p2made/P2-Camp-Kitchen/docs/Sheet-Metal.pdf

1. Number Plate Mount
2. Battery Clamp
3. Fridge Tray Rails
4. Stainless Steel Top
5. Splash Back Cover

To be attached to the back frame. Drawn as 1 mm sheet metal.

# Sheet Metal

# Number Plate Mount

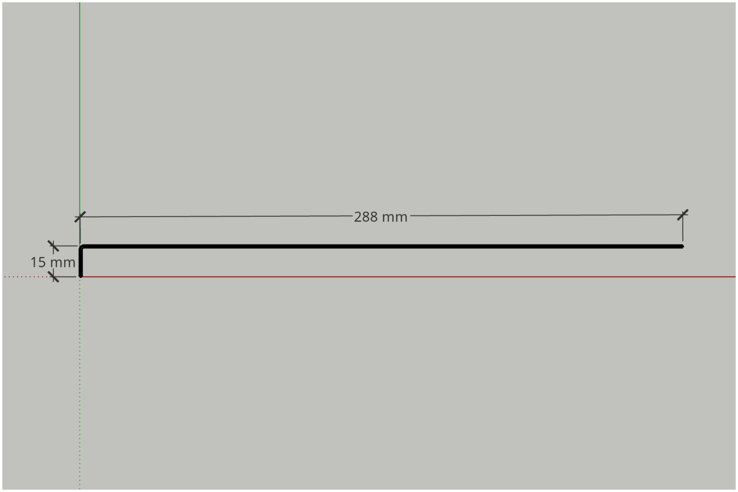
[picture p41: figure]
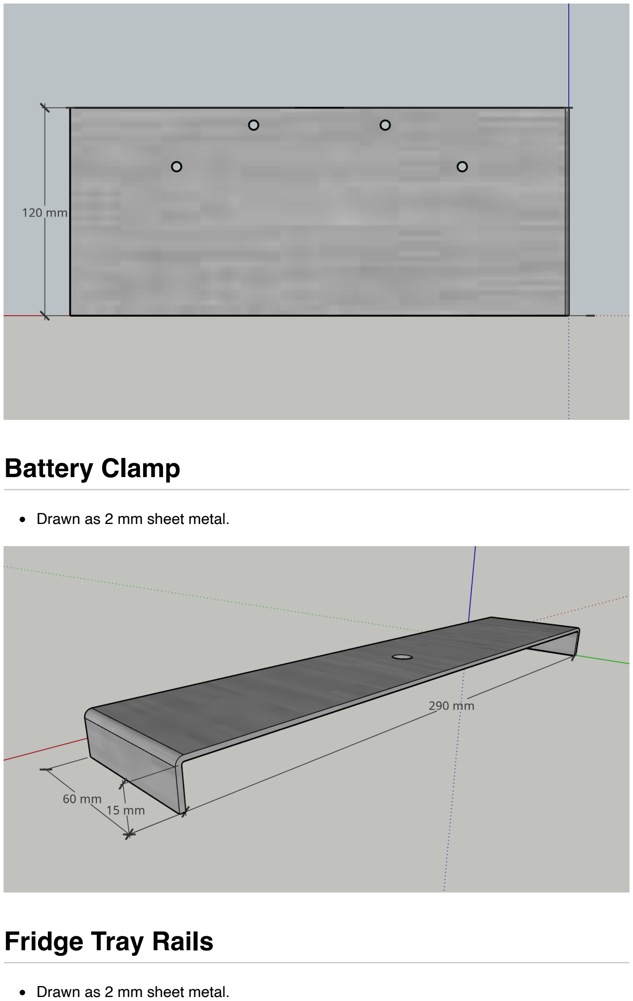
[picture p42: page 2]

Drawn as 2 mm sheet metal.

Drawn as 2 mm sheet metal.

# Battery Clamp

# Fridge Tray Rails

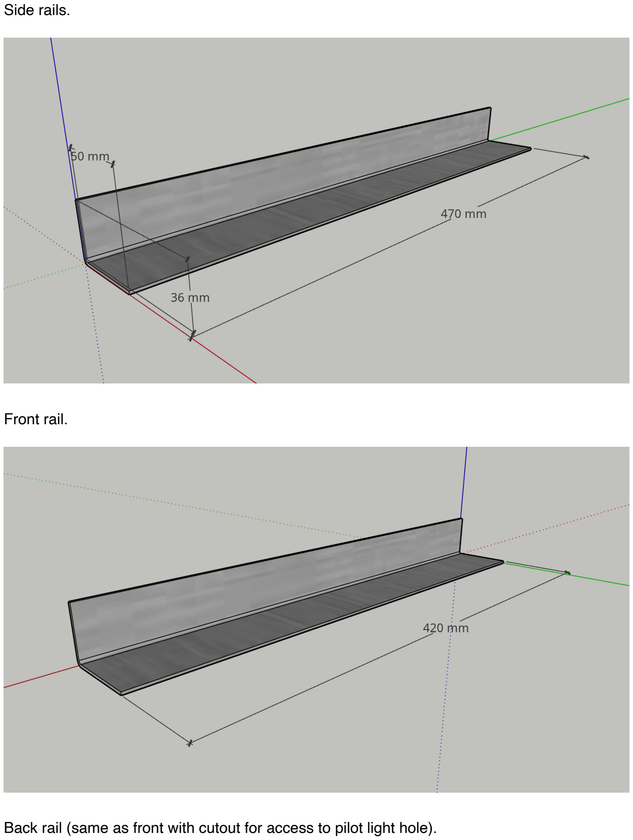
[picture p43: page 3]

Side rails.

Front rail.

Back rail (same as front with cutout for access to pilot light hole).

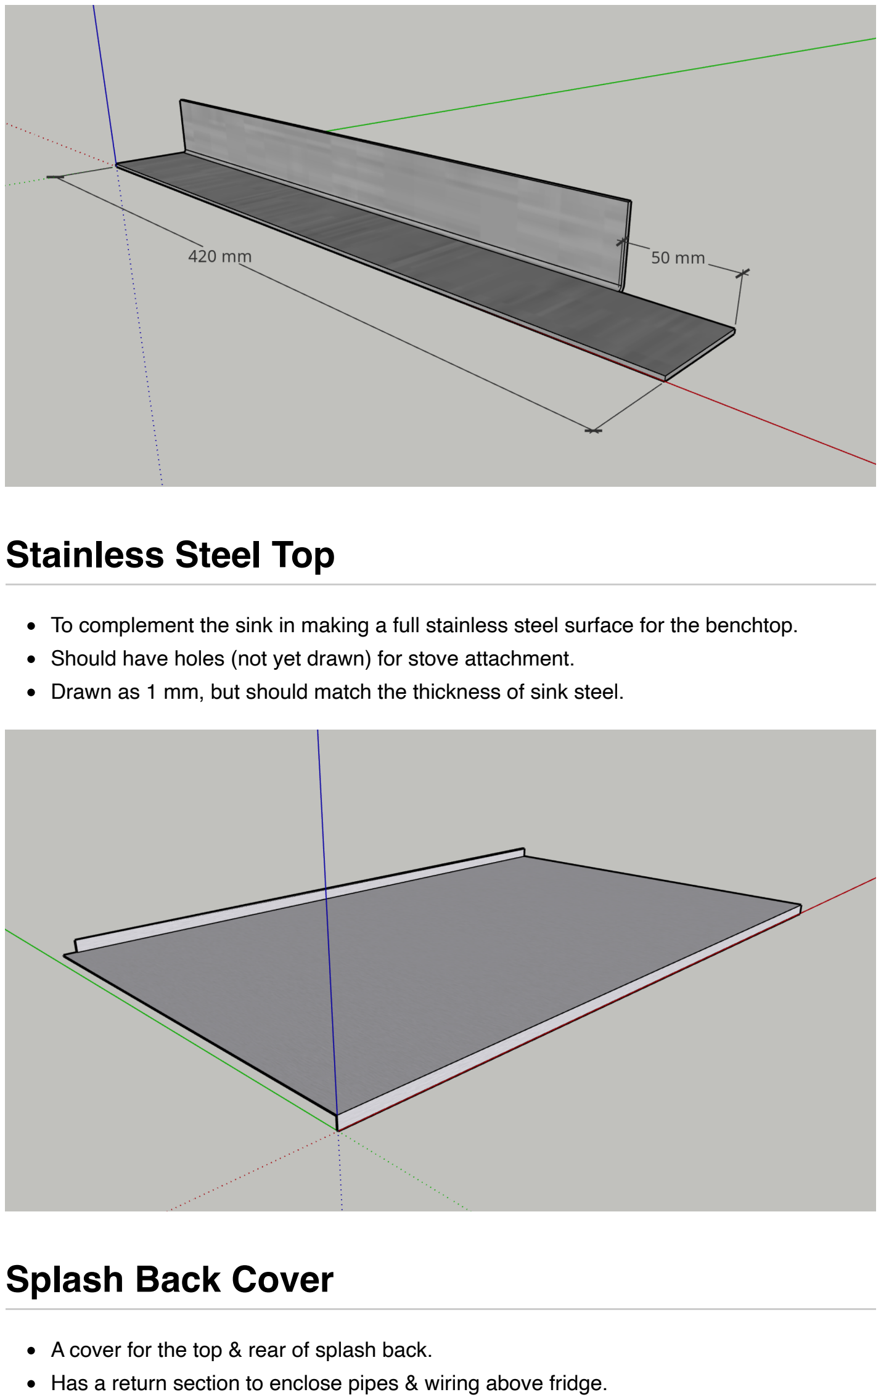
[picture p44: page 4]

To complement the sink in making a full stainless steel surface for the benchtop. Should have holes (not yet drawn) for stove attachment.
Drawn as 1 mm, but should match the thickness of sink steel.

A cover for the top & rear of splash back.
Has a return section to enclose pipes & wiring above fridge.

# Stainless Steel Top

# Splash Back Cover

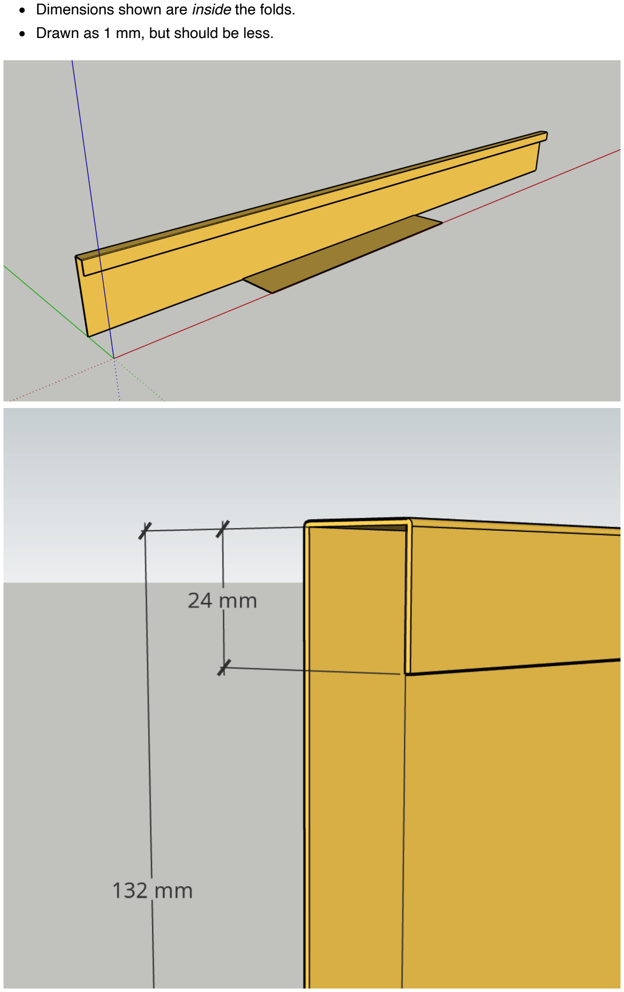
[picture p45: page 5]

Dimensions shown are inside the folds. Drawn as 1 mm, but should be less.

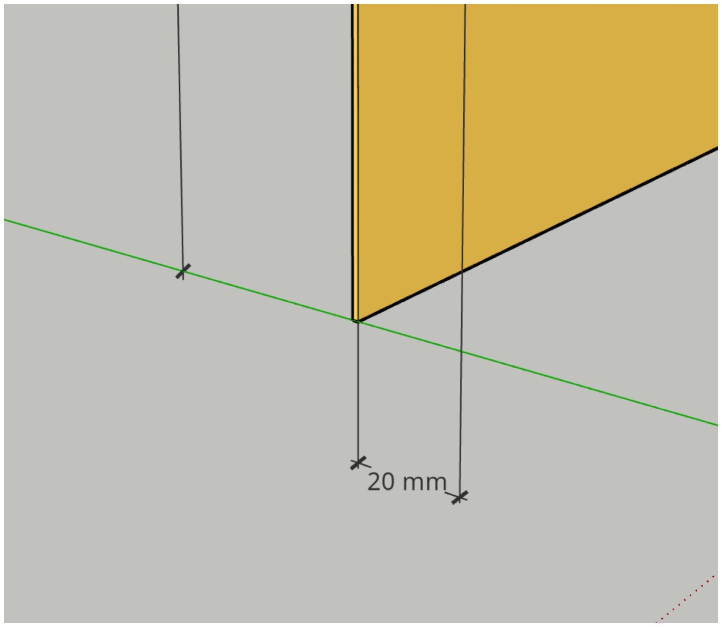
[picture p46: figure]
