p2made/P2-Camp-Kitchen/docs/Overview/04-Back.pdf

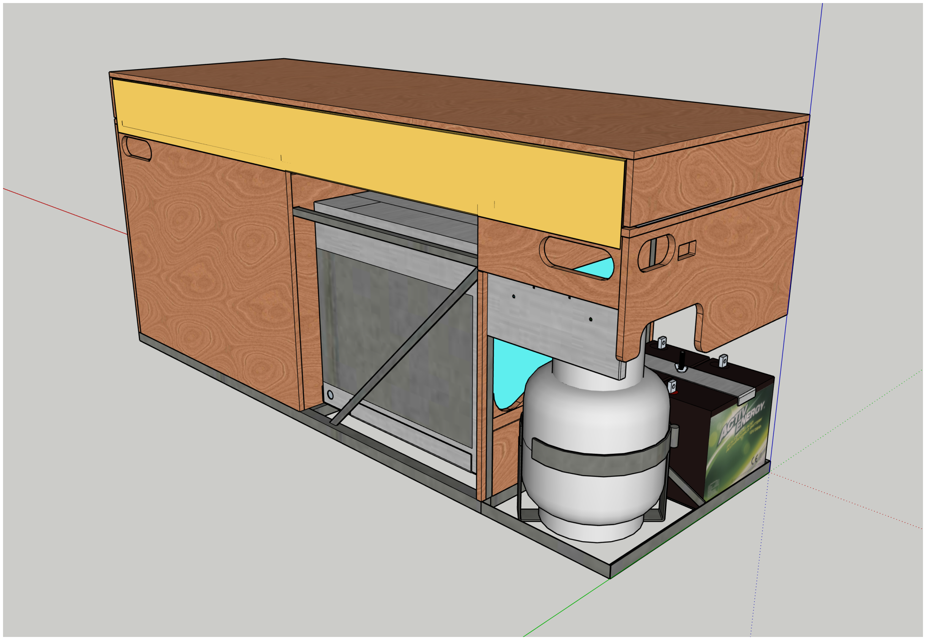
[picture p59: page 1]
