p2made/P2-Camp-Kitchen/docs/Overview/05-Open-Left.pdf

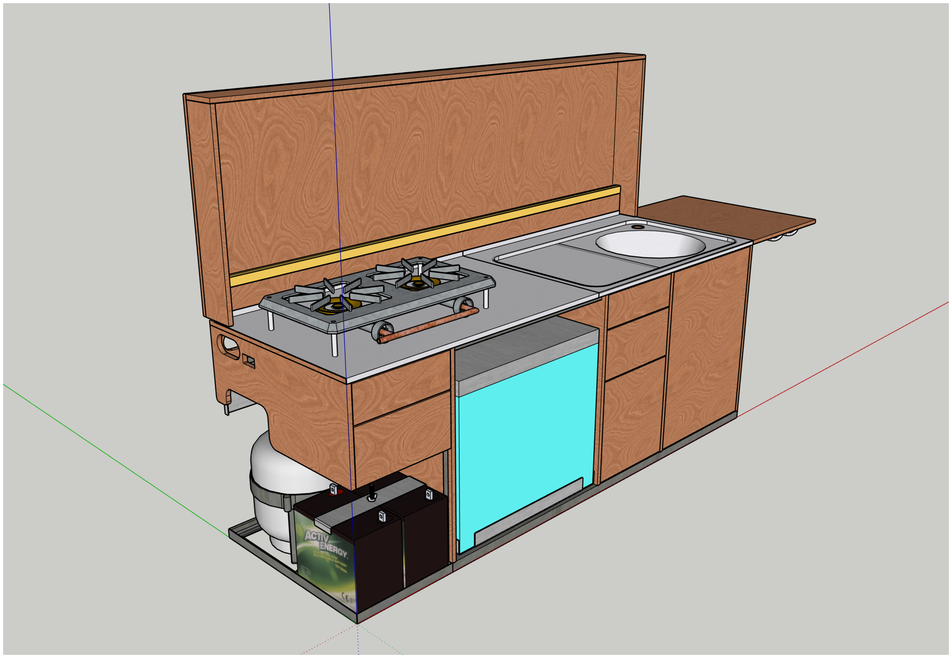
[picture p60: page 1]
