p2made/P2-Camp-Kitchen/docs/Overview/06-Open-Right.pdf

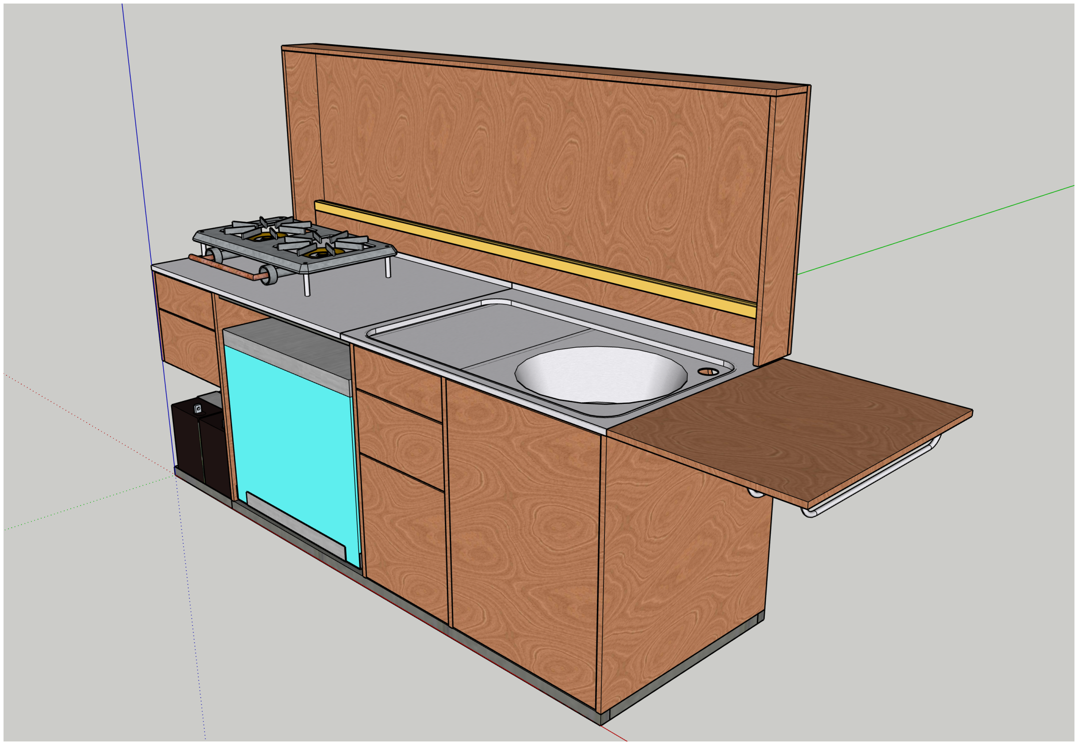
[picture p61: page 1]
