p2made/P2-Camp-Kitchen/docs/Plywood/01-End-Panel-LH.pdf

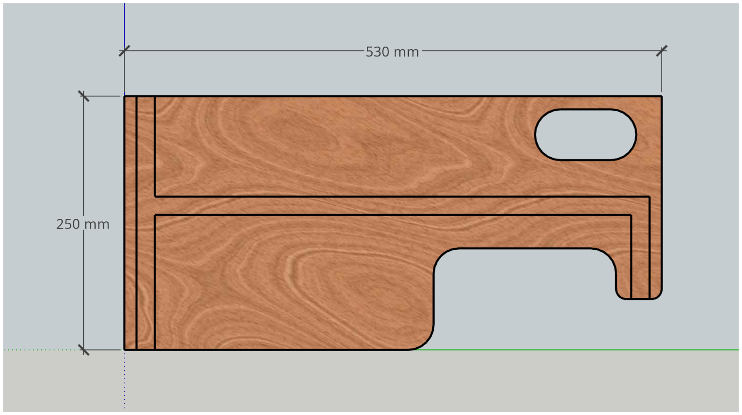
[picture p62: page 1]
