p2made/P2-Camp-Kitchen/docs/Plywood/02-End-Panel-RH.pdf

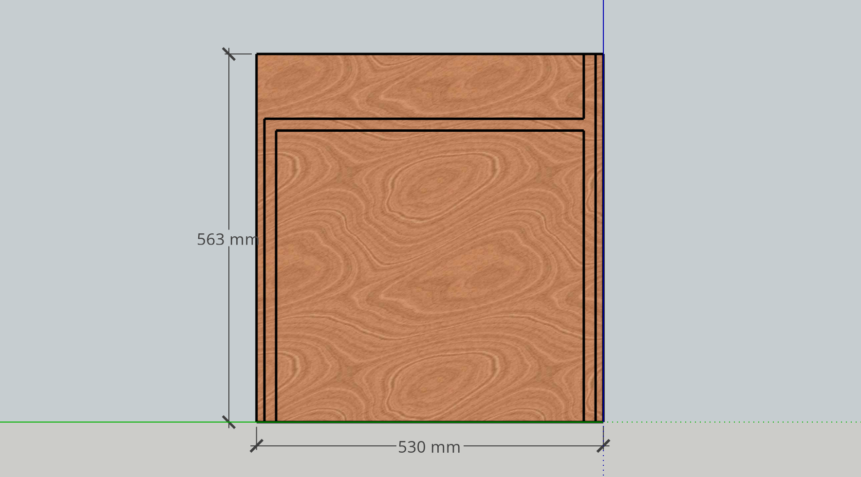
[picture p63: page 1]
