p2made/P2-Camp-Kitchen/docs/Frame/01-Frame-Front.pdf

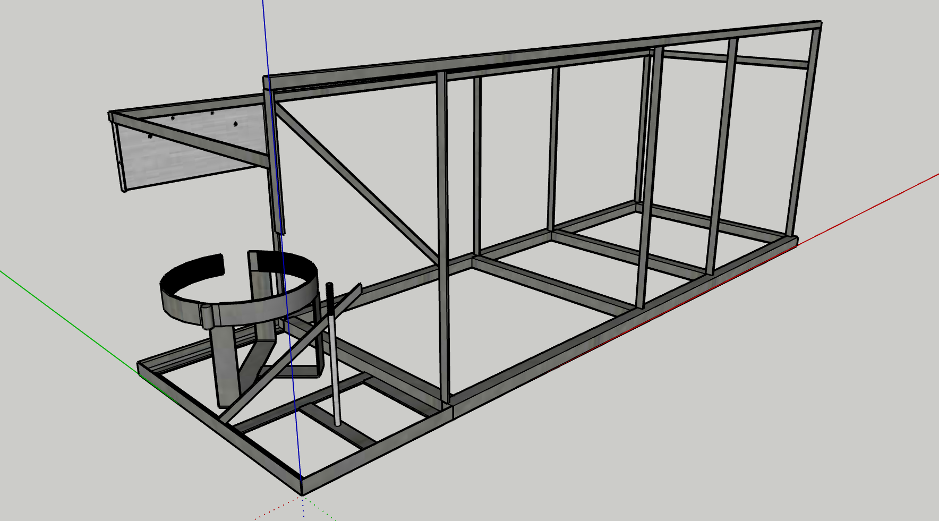
[picture p64: page 1]
