p2made/P2-Camp-Kitchen/docs/Frame/02-Frame-Back.pdf

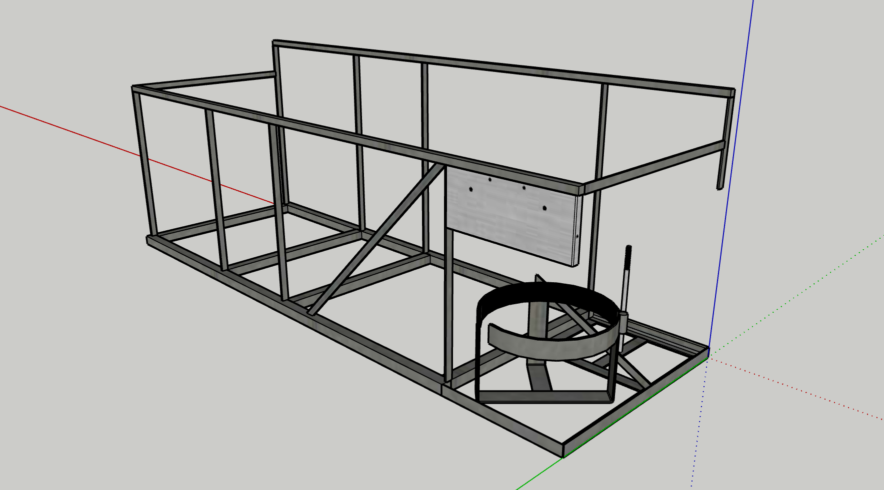
[picture p65: page 1]
