p2made/P2-Camp-Kitchen/docs/Undercarriage/05-Under-Frame-Dimensioned.pdf

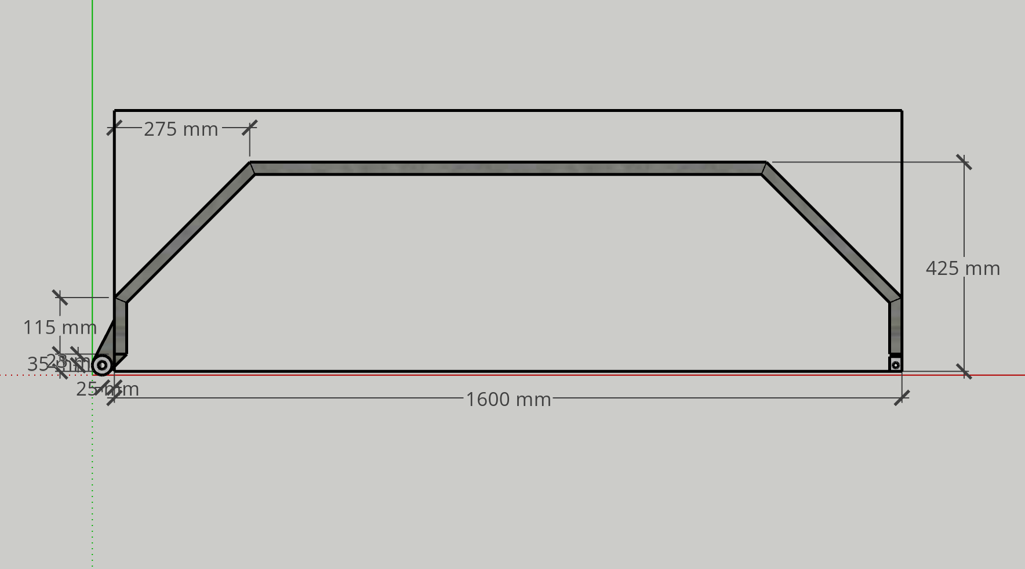
[picture p66: page 1]
