p2made/P2-Camp-Kitchen/docs/Undercarriage/06-Under-Frame-Detail.pdf

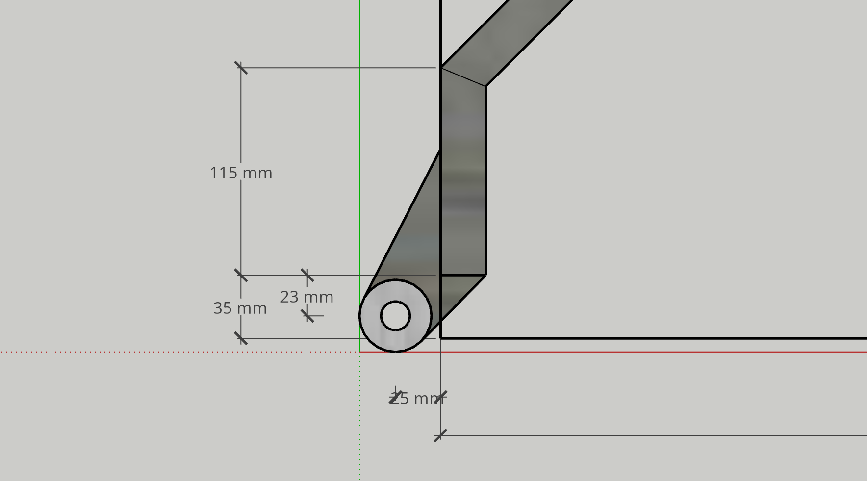
[picture p67: page 1]
