p2made/P2-Camp-Kitchen/docs/Undercarriage/03-Base-Dimensioned.pdf

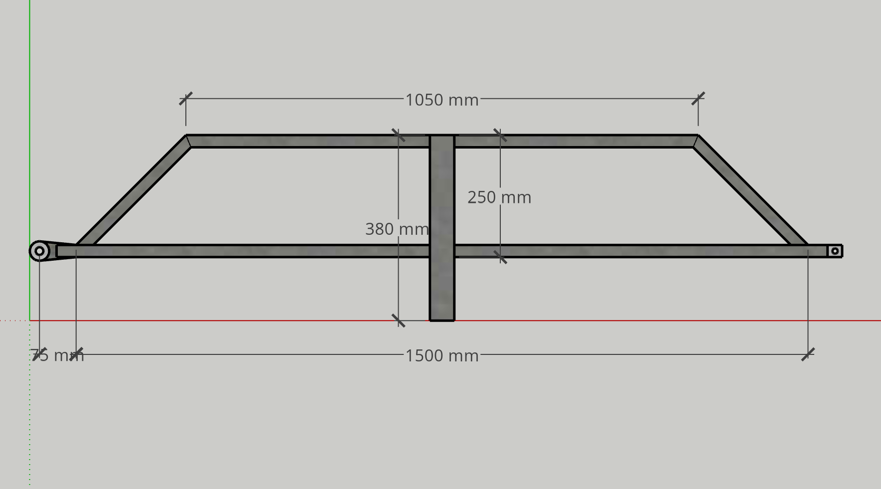
[picture p68: page 1]
