p2made/P2-Camp-Kitchen/docs/Undercarriage/03a-Base-Dimensioned-Alternate.pdf

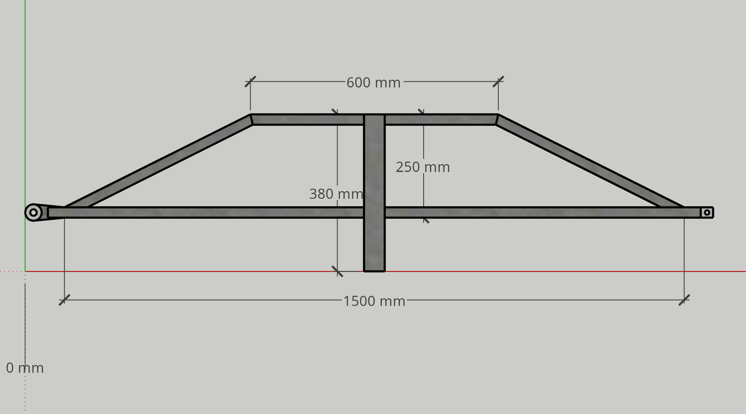
[picture p69: page 1]
