p2made/P2-Camp-Kitchen/docs/Sheet-Metal/02-Number-Plate-Mount-Back.pdf

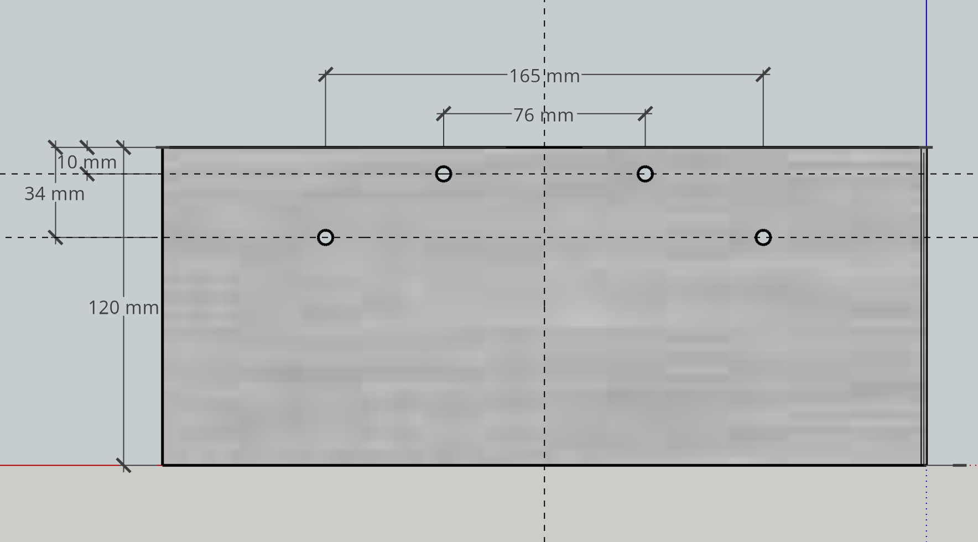
[picture p70: page 1]
