p2made/P2-Camp-Kitchen/docs/Sheet-Metal/01-Number-Plate-Mount-Top.pdf

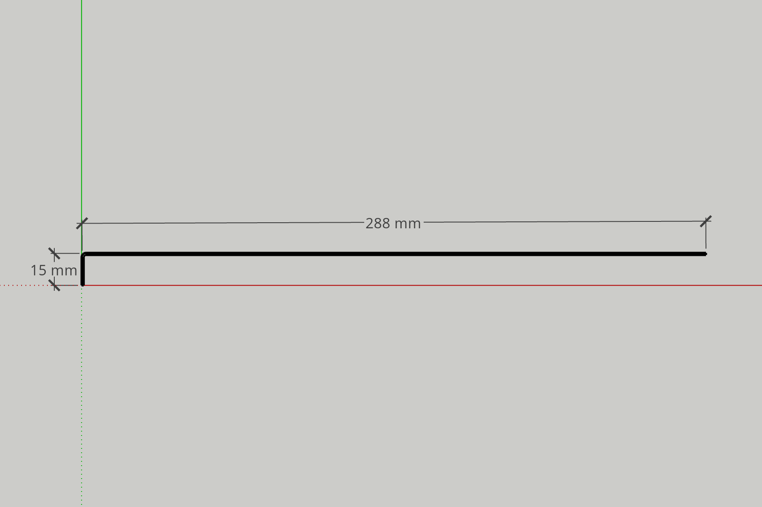
[picture p71: page 1]
