p2made/P2-Camp-Kitchen/docs/Detail/01-Front.pdf

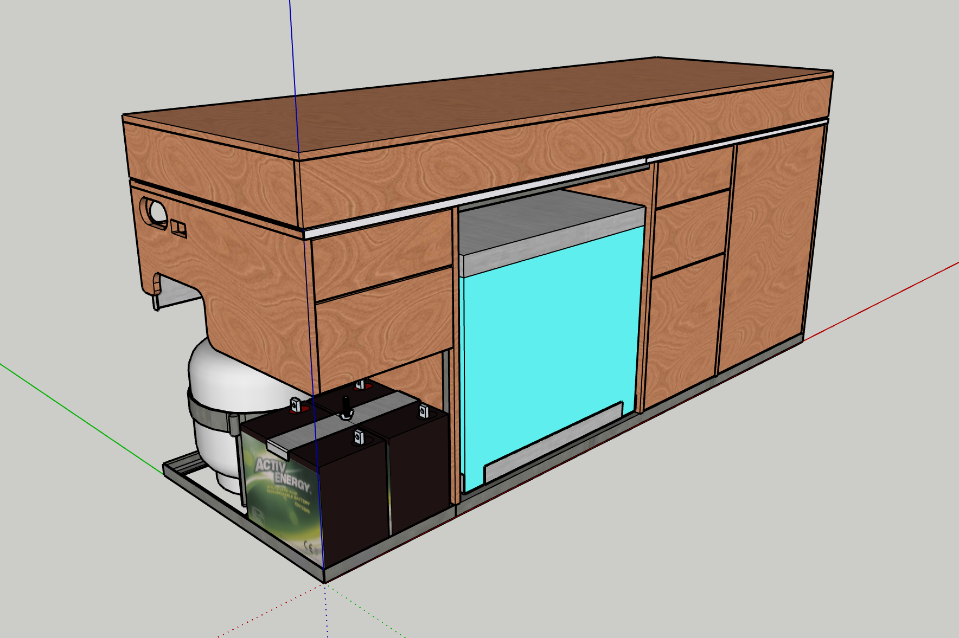
[picture p72: page 1]
