p2made/P2-Camp-Kitchen/docs/Detail/02-Back.pdf

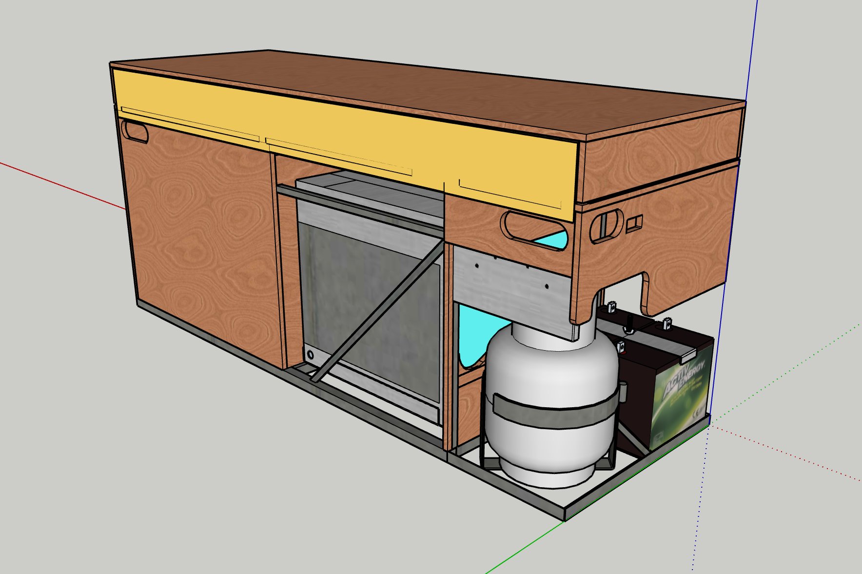
[picture p73: page 1]
