p2made/P2-Camp-Kitchen/docs/Detail/03-Open-Left.pdf

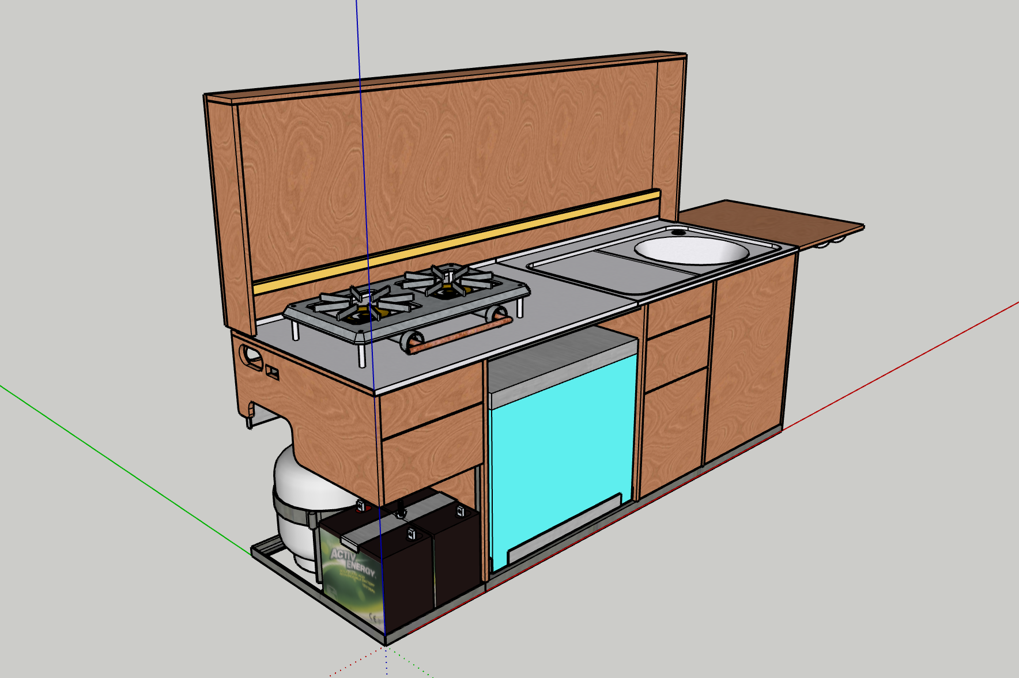
[picture p74: page 1]
