p2made/P2-Camp-Kitchen/docs/Detail/04-Open-Right.pdf

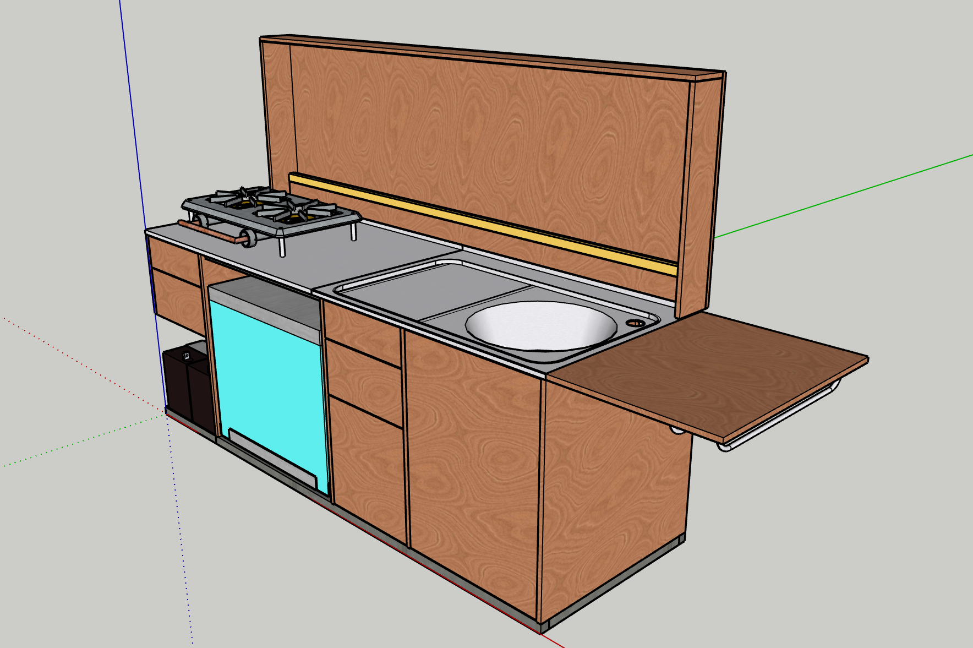
[picture p75: page 1]
