p2made/P2-Camp-Kitchen/docs/Detail/05-Lid-Closed.pdf

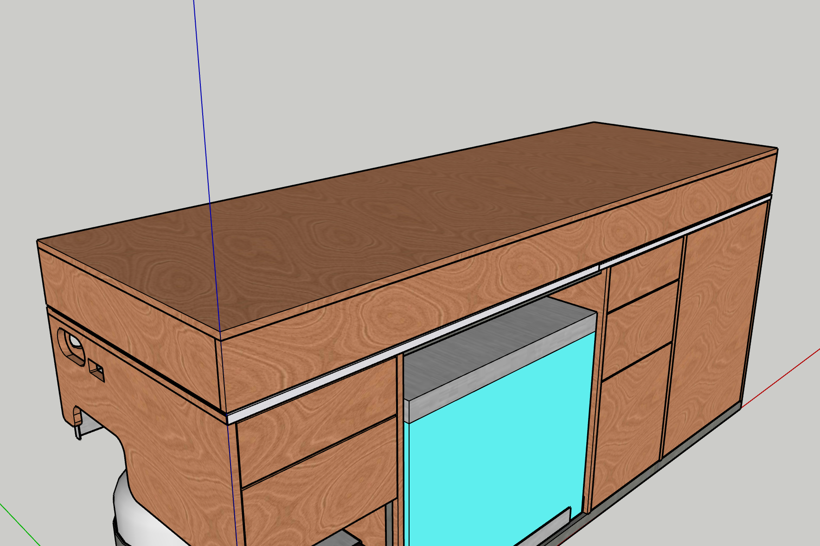
[picture p76: page 1]
