p2made/P2-Camp-Kitchen/docs/Detail/06-Lid-Open.pdf

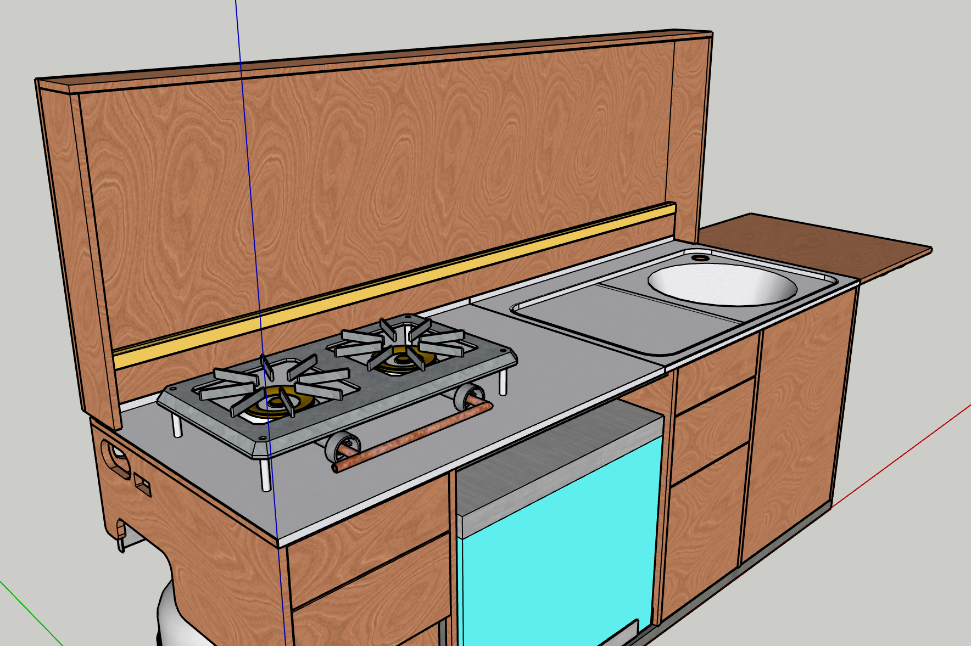
[picture p77: page 1]
