p2made/P2-Camp-Kitchen/docs/Detail/08-Stove-Detail.pdf

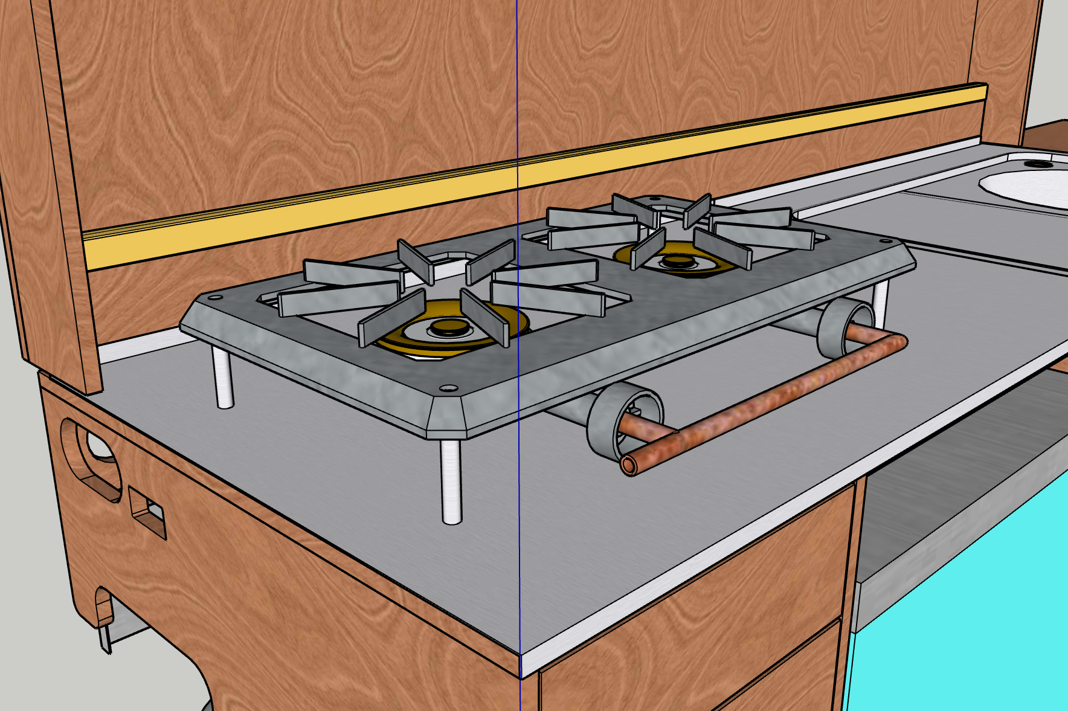
[picture p78: page 1]
