p2made/P2-Camp-Kitchen/docs/Detail/09-Sink-Detail.pdf

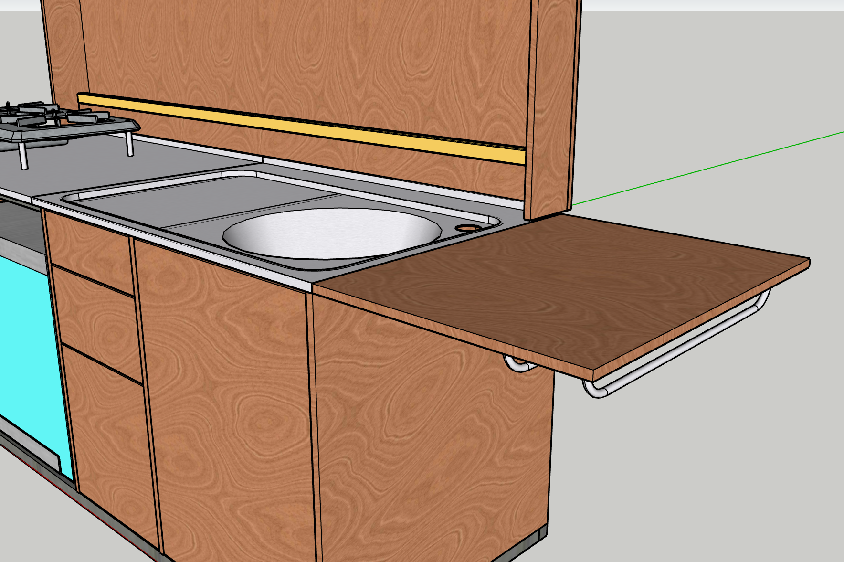
[picture p79: page 1]
