p2made/P2-Camp-Kitchen/docs/Detail/10-Subframe-Front.pdf

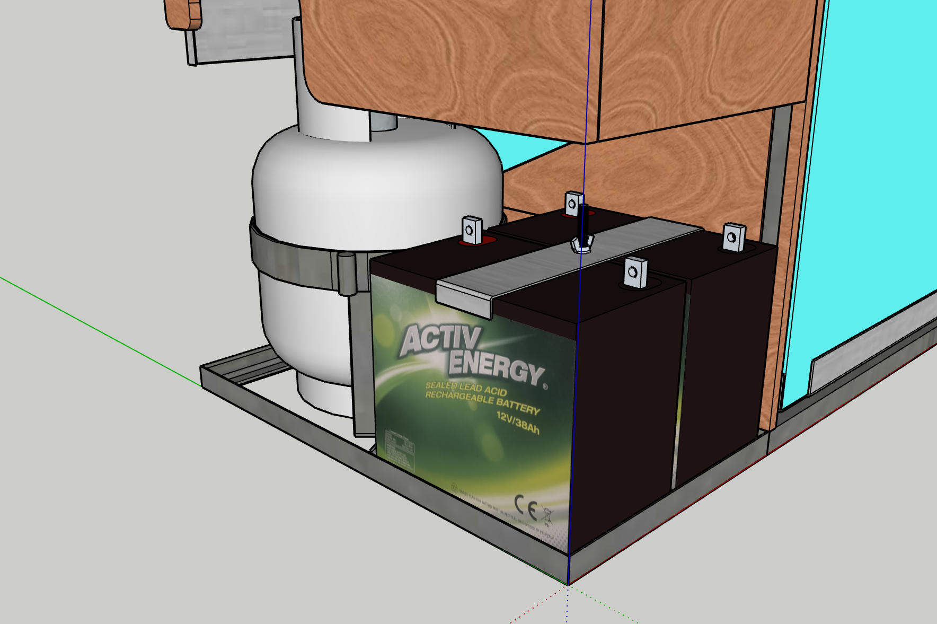
[picture p80: page 1]
