p2made/P2-Camp-Kitchen/docs/Detail/11-Subframe-Back.pdf

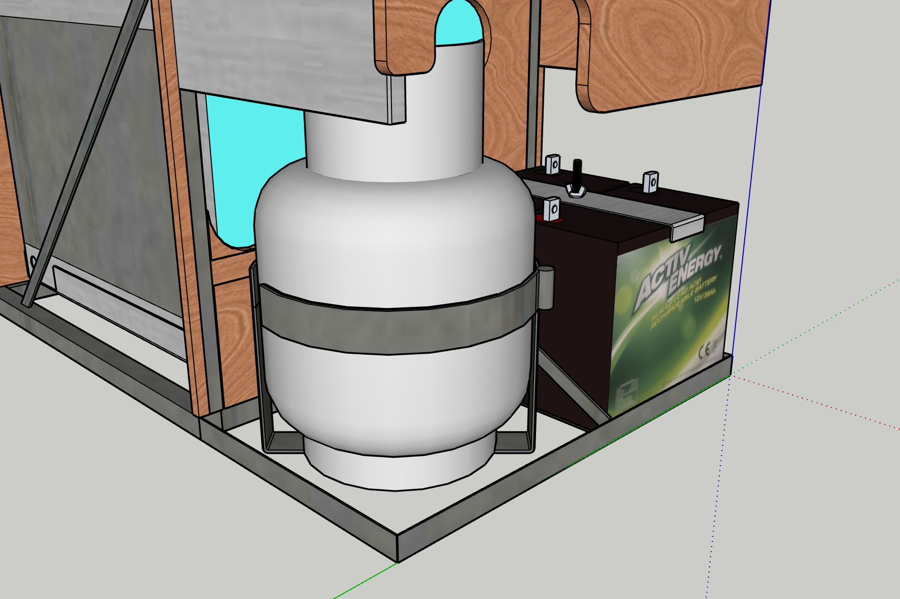
[picture p81: page 1]
