p2made/P2-Camp-Kitchen/docs/Frame/03-Bottom-Frame.pdf

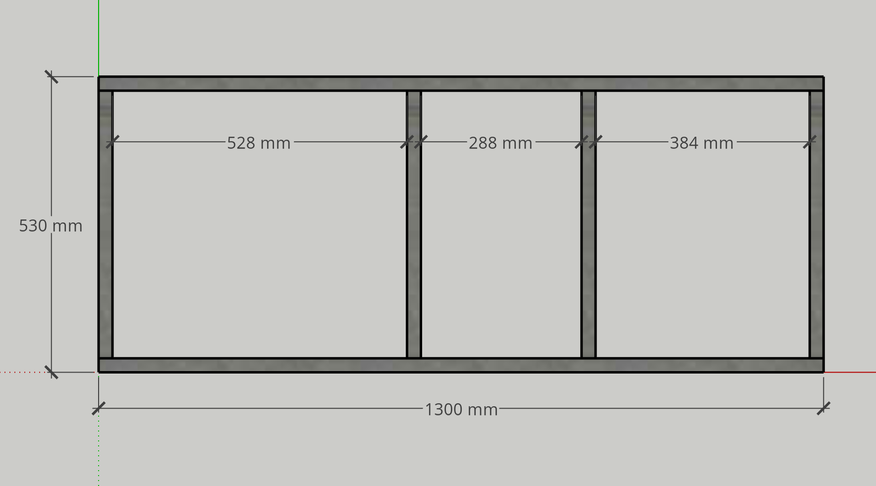
[picture p82: page 1]
