p2made/P2-Camp-Kitchen/docs/Frame/05-Back-Frame.pdf

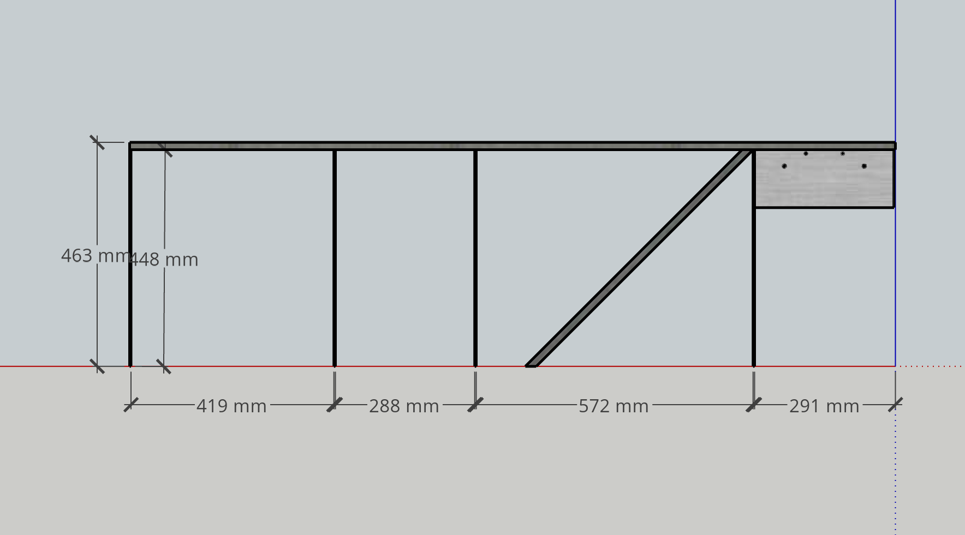
[picture p83: page 1]
