p2made/P2-Camp-Kitchen/docs/Frame/08-Energy-Subframe-Plan-View.pdf

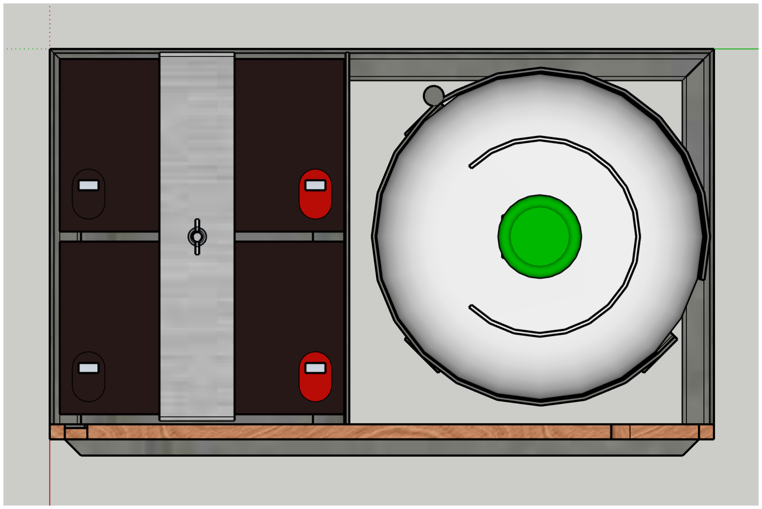
[picture p84: page 1]
