p2made/P2-Camp-Kitchen/docs/Frame/09-Energy-Subframe-2-Plan-View.pdf

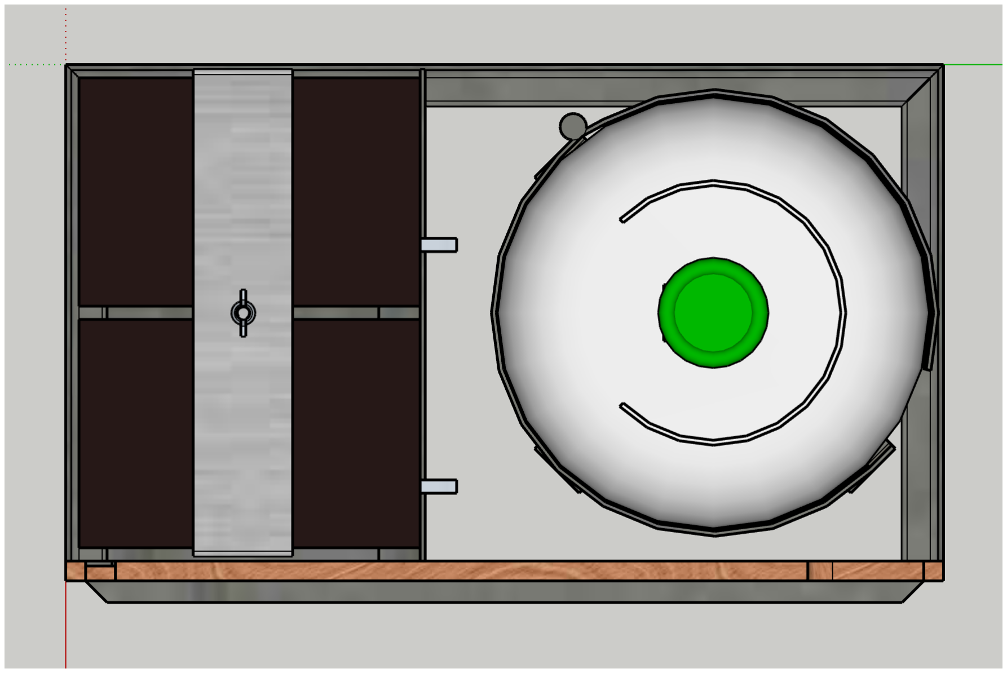
[picture p85: page 1]
