p2made/P2-Camp-Kitchen/docs/Plywood/06-Back-Panel-LH.pdf

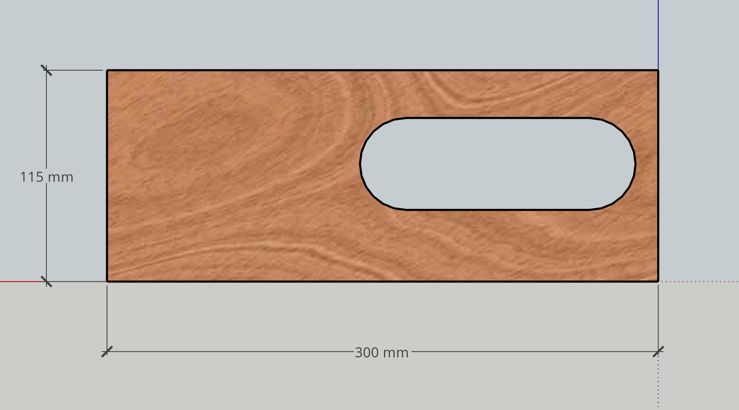
[picture p86: page 1]
