p2made/P2-Camp-Kitchen/docs/Plywood/07-Back-Panel-RH.pdf

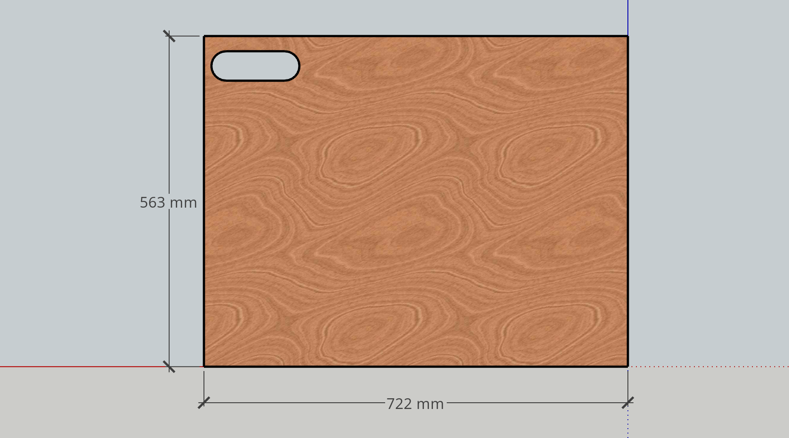
[picture p87: page 1]
