p2made/P2-Camp-Kitchen/docs/Sheet-Metal/03-Battery-Clamp.pdf

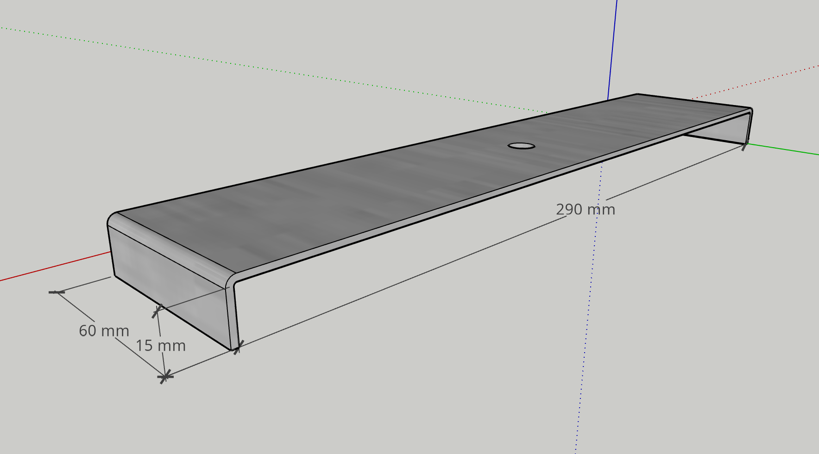
[picture p88: page 1]
