p2made/P2-Camp-Kitchen/docs/Sheet-Metal/04-Fridge-Tray-Side-Rail.pdf

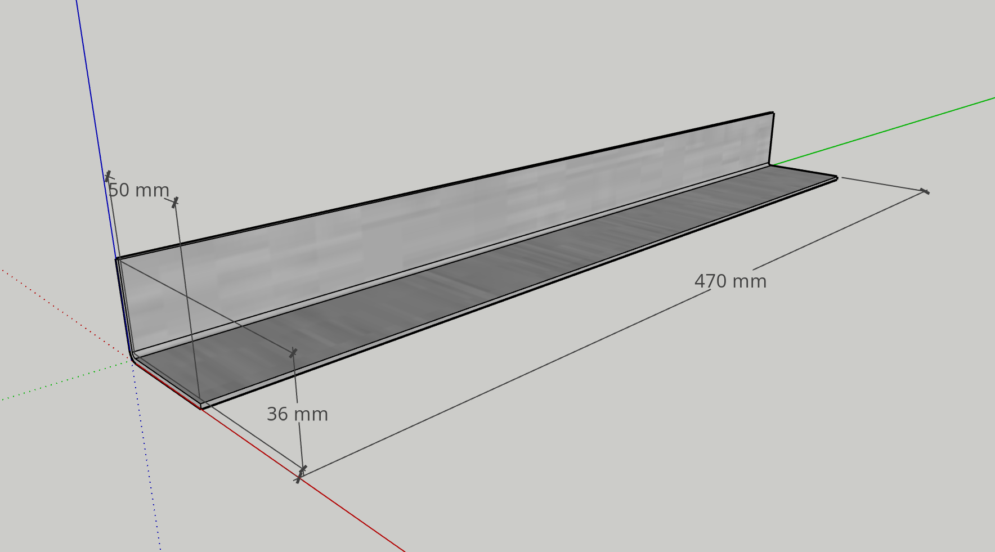
[picture p89: page 1]
