p2made/P2-Camp-Kitchen/docs/Sheet-Metal/05-Fridge-Tray-Front-Rail.pdf

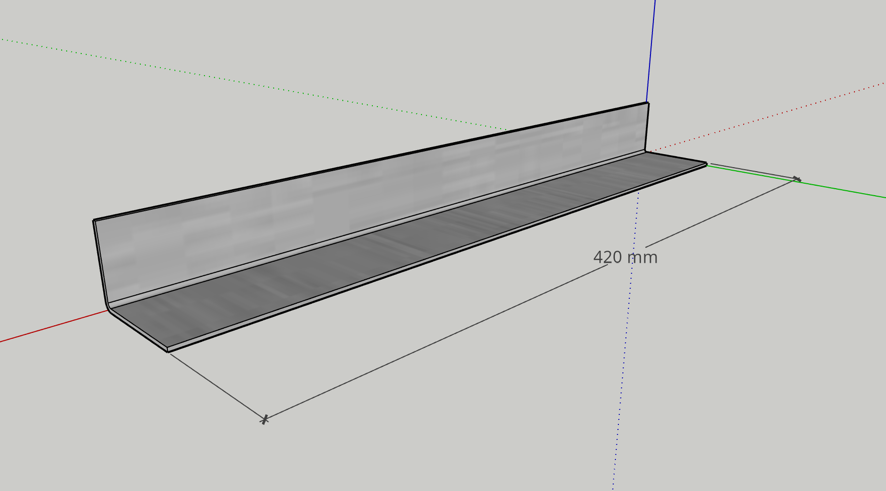
[picture p90: page 1]
