p2made/P2-Camp-Kitchen/docs/Sheet-Metal/06-Fridge-Tray-Back-Rail.pdf

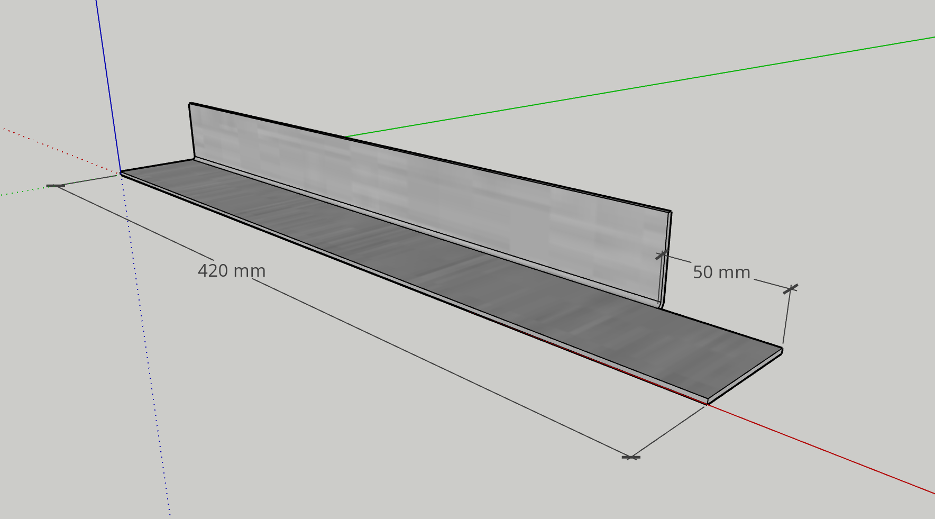
[picture p91: page 1]
