p2made/P2-Camp-Kitchen/docs/Sheet-Metal/07-Stainless-Steel-Top.pdf

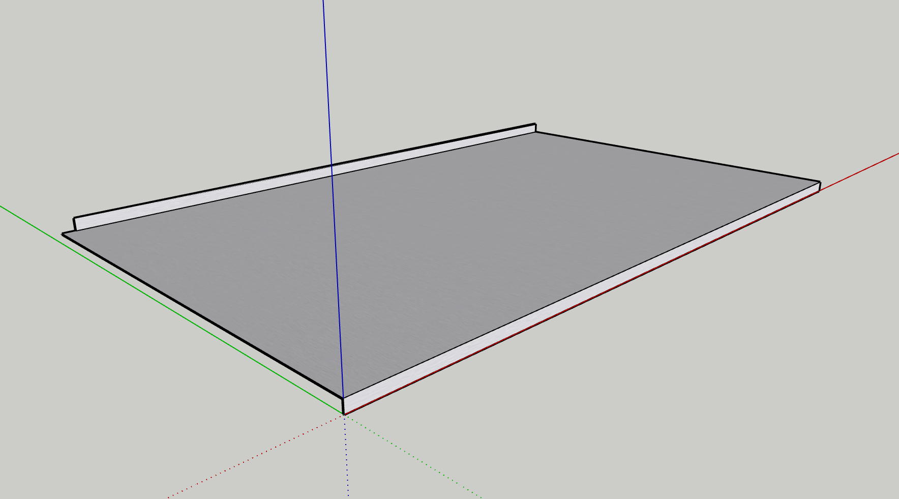
[picture p92: page 1]
