p2made/P2-Camp-Kitchen/docs/Sheet-Metal/08-Splash-Back-Cover.pdf

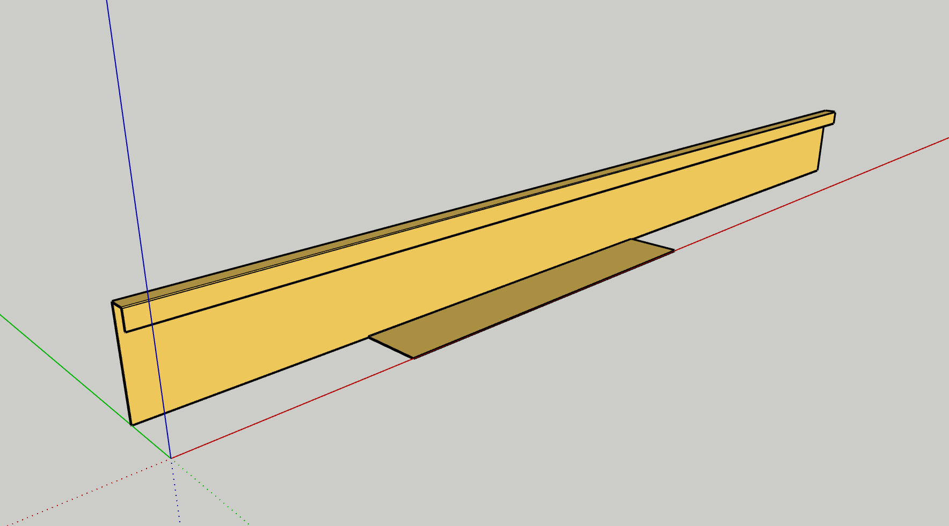
[picture p93: page 1]
