p2made/P2-Camp-Kitchen/docs/Sheet-Metal/09-Splash-Back-Cover-End.pdf

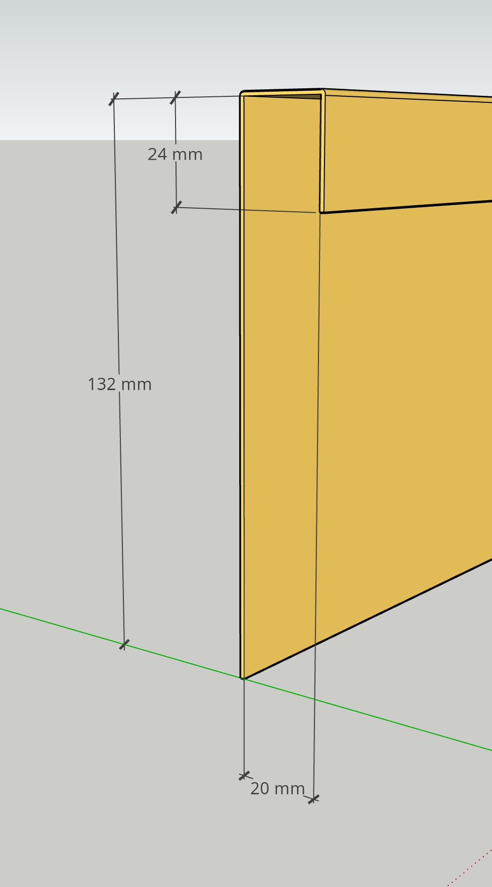
[picture p94: page 1]
