p2made/P2-Camp-Kitchen/docs/Undercarriage/01-Under-Frame-Base.pdf

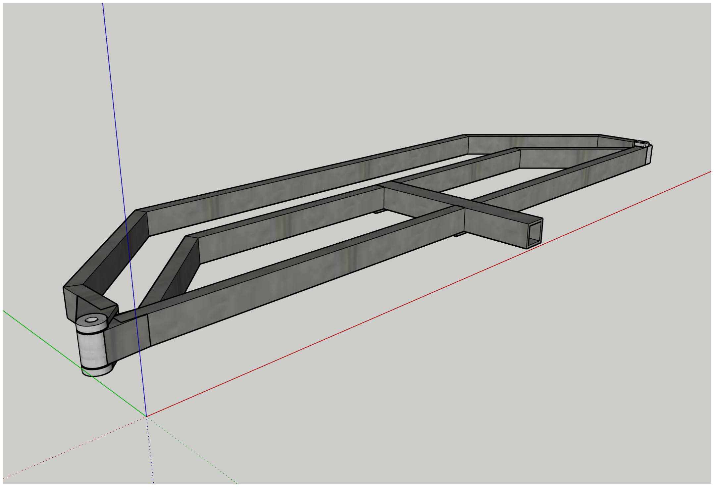
[picture p95: page 1]
