p2made/P2-Camp-Kitchen/docs/Undercarriage/02-Base.pdf

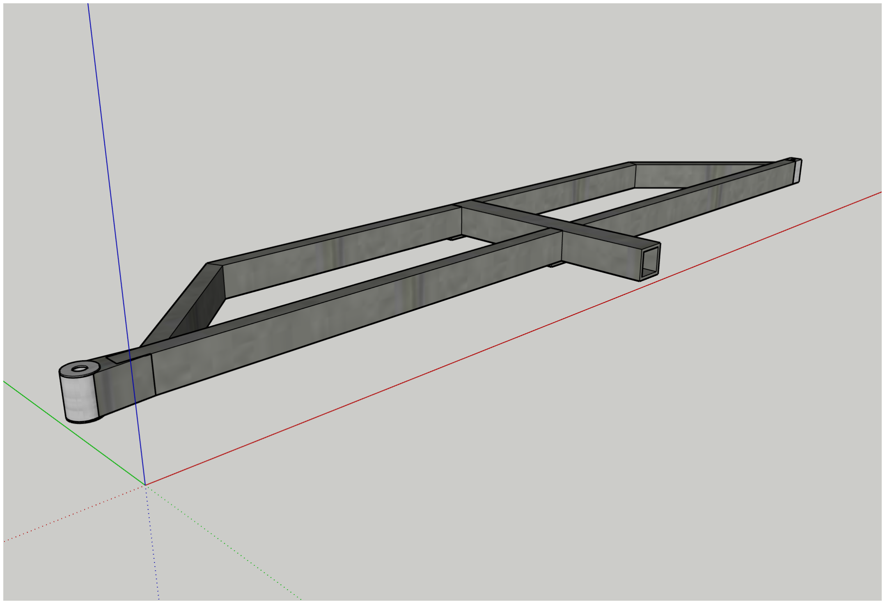
[picture p96: page 1]
