p2made/P2-Camp-Kitchen/docs/Undercarriage/04-Under-Frame.pdf

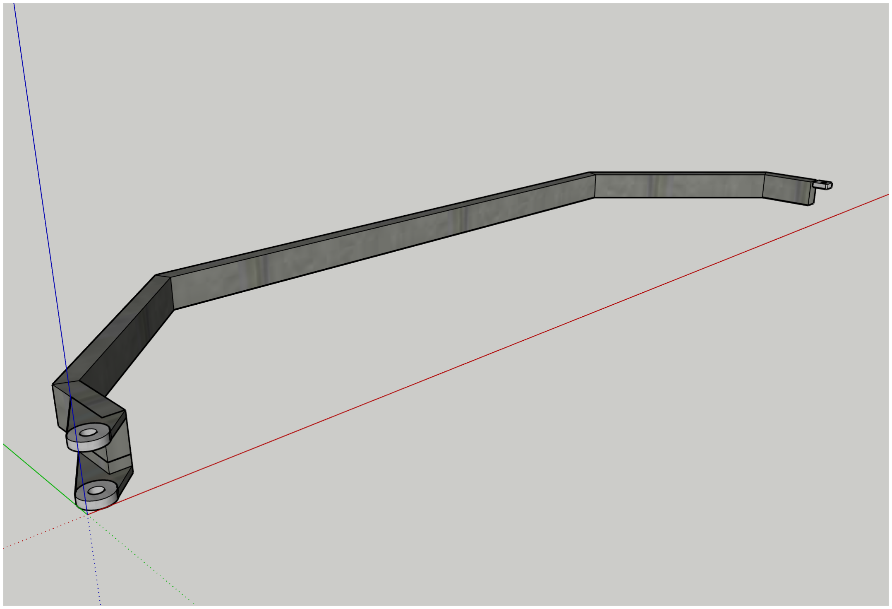
[picture p97: page 1]
