p2made/P2-Camp-Kitchen/docs/Undercarriage/07-Base-Pivot.pdf

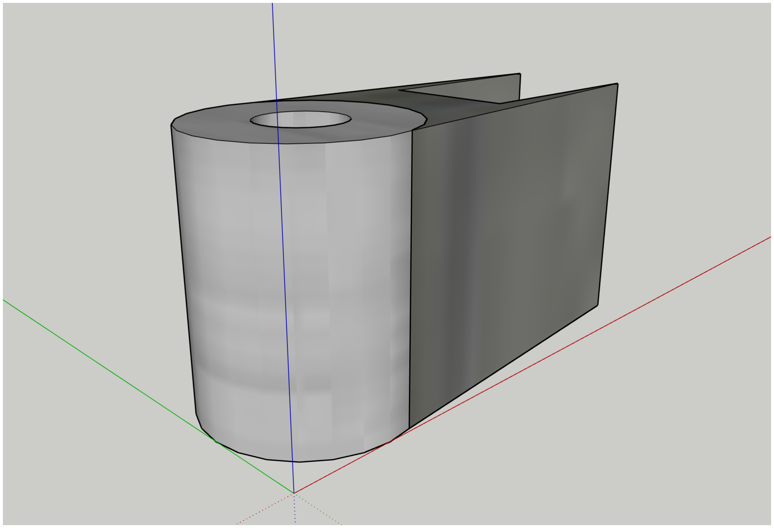
[picture p98: page 1]
