p2made/P2-Camp-Kitchen/docs/Undercarriage/08-Pivot-Top.pdf

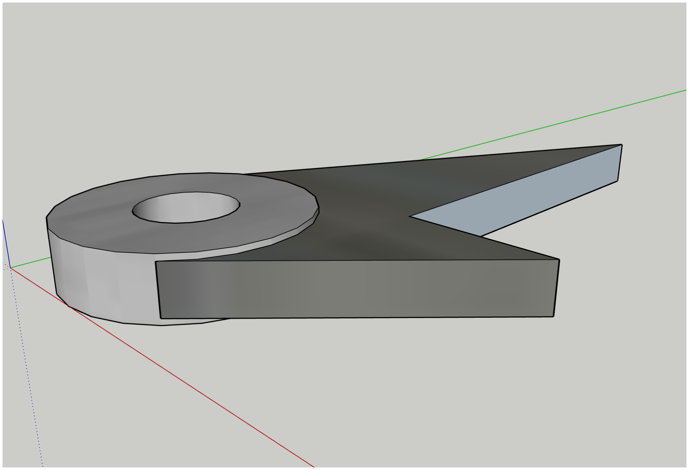
[picture p99: page 1]
