p2made/P2-Camp-Kitchen/docs/Undercarriage/09-Pivot-Bottom.pdf

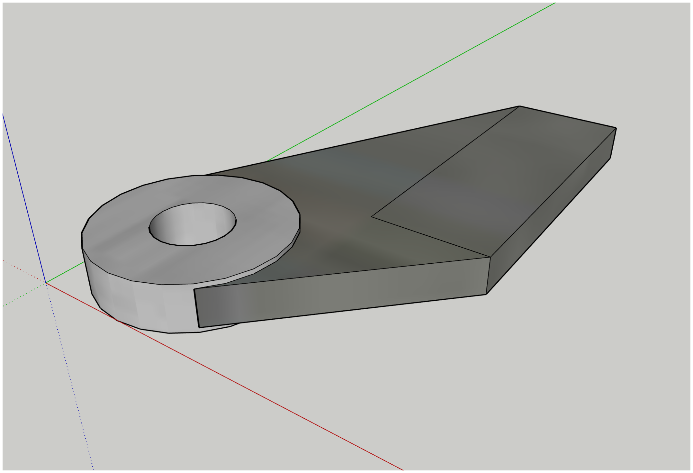
[picture p100: page 1]
