p2made/P2-Camp-Kitchen/docs/Undercarriage/10-Pivot-Spacer.pdf

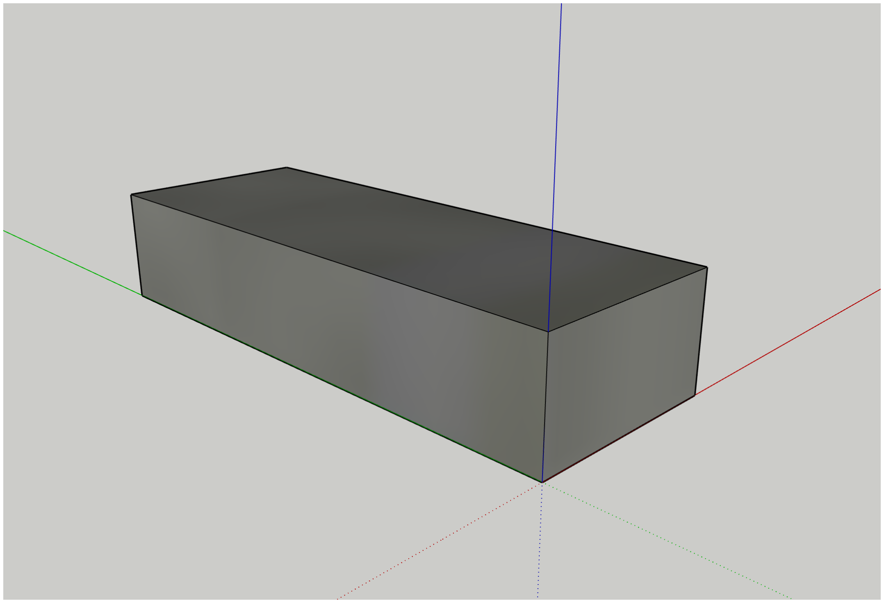
[picture p101: page 1]
