p2made/P2-Camp-Kitchen/docs/Frame/04-Front-Frame.pdf

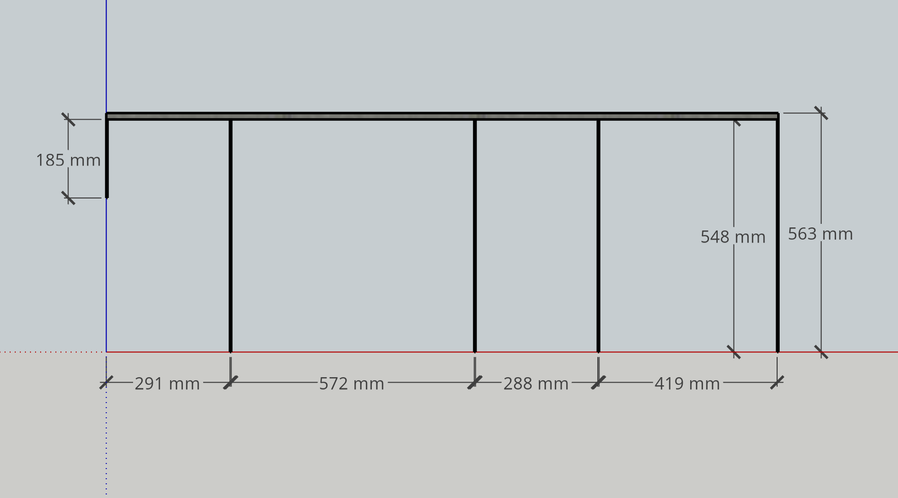
[picture p102: page 1]
