p2made/P2-Camp-Kitchen/docs/Frame/06-Energy-Subframe-FL.pdf

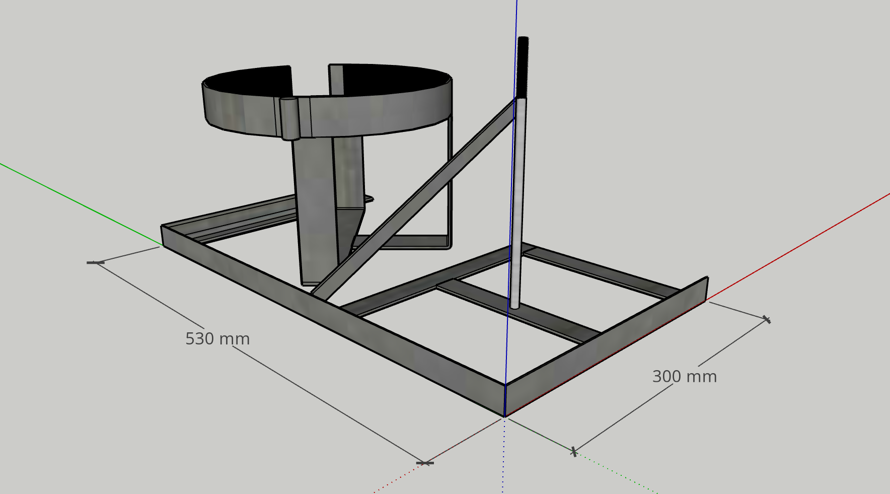
[picture p103: page 1]
