p2made/P2-Camp-Kitchen/docs/Frame/07-Energy-Subframe-FR.pdf

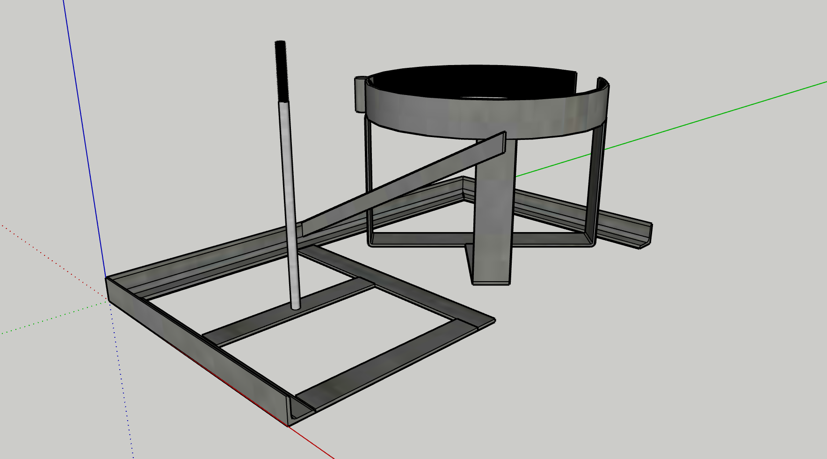
[picture p104: page 1]
