p2made/P2-Camp-Kitchen/docs/Plywood/03-Cross-Panel-1.pdf

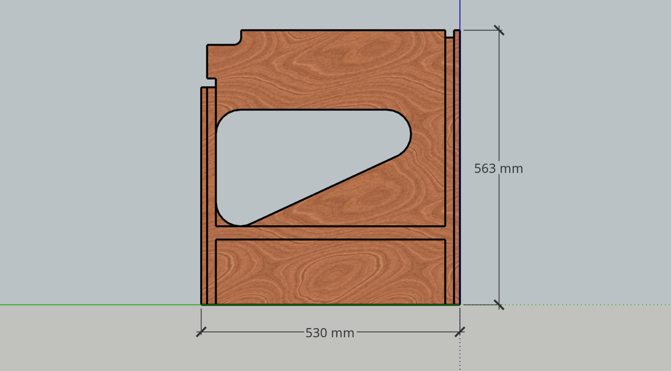
[picture p105: page 1]
