p2made/P2-Camp-Kitchen/docs/Plywood/04-Cross-Panel-2.pdf

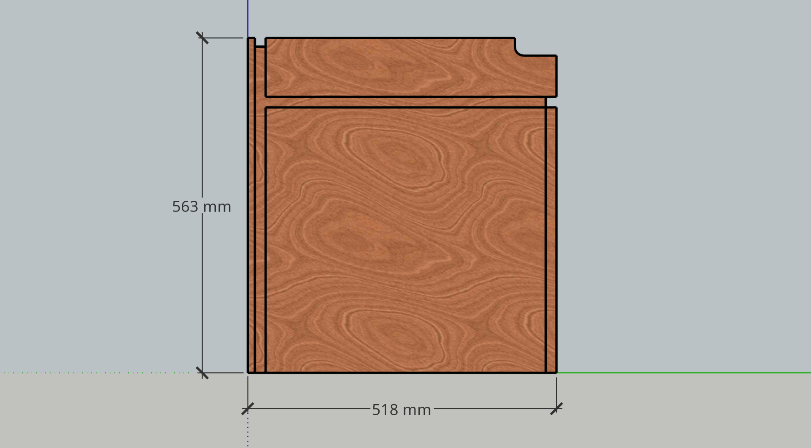
[picture p106: page 1]
