p2made/P2-Camp-Kitchen/docs/Plywood/05-Cross-Panel-3.pdf

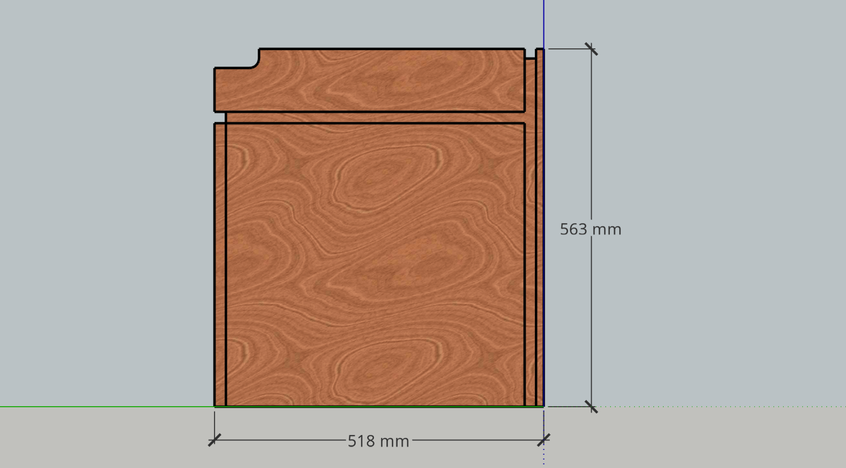
[picture p107: page 1]
