p2made/P2-Camp-Kitchen/docs/Plywood/08-Benchtop.pdf

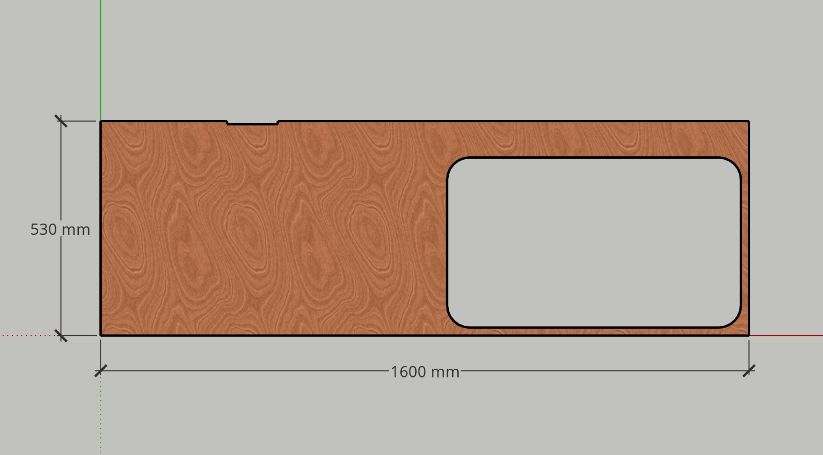
[picture p108: page 1]
