p2made/P2-Camp-Kitchen/docs/Plywood/13-Cupboard-Floor.pdf

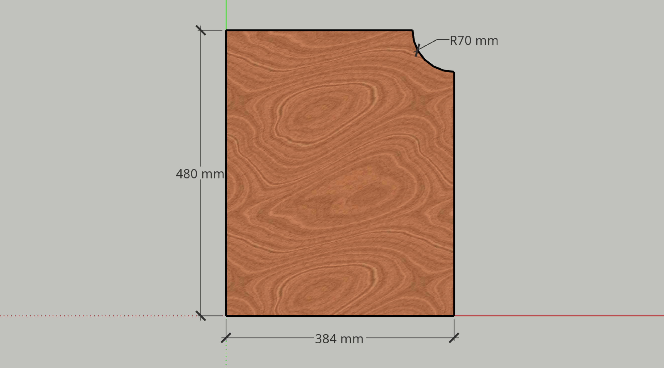
[picture p109: page 1]
