p2made/P2-Camp-Kitchen/docs/Plywood/14-Cupboard-Shelf.pdf

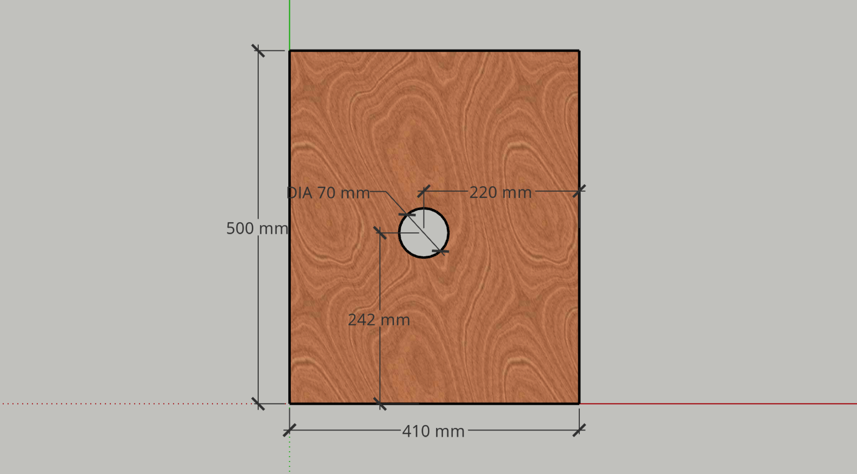
[picture p110: page 1]
