p2made/P2-Camp-Kitchen/docs/Undercarriage/07-Base-Pivot.png

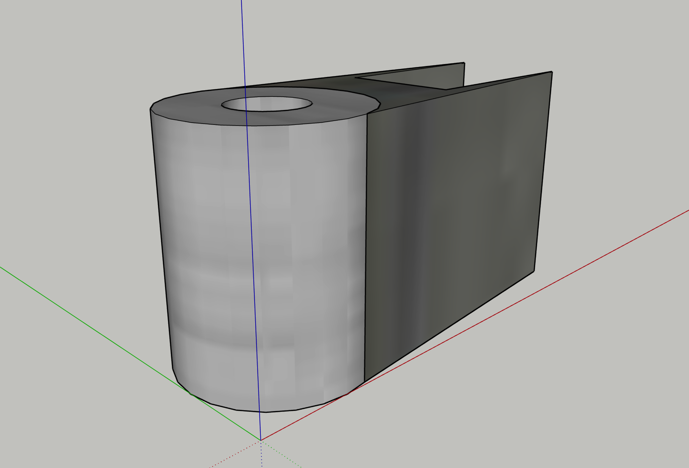
docs/Undercarriage/07-Base-Pivot.png
