p2made/P2-Camp-Kitchen/docs/Undercarriage/08-Pivot-Top.png

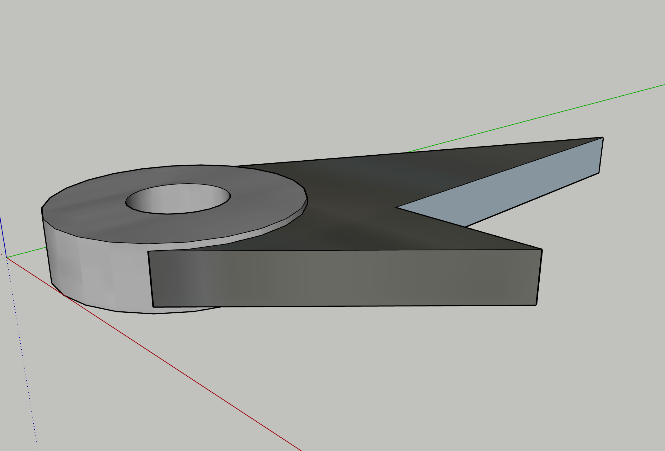
docs/Undercarriage/08-Pivot-Top.png
