p2made/P2-Camp-Kitchen/docs/Undercarriage/09-Pivot-Bottom.png

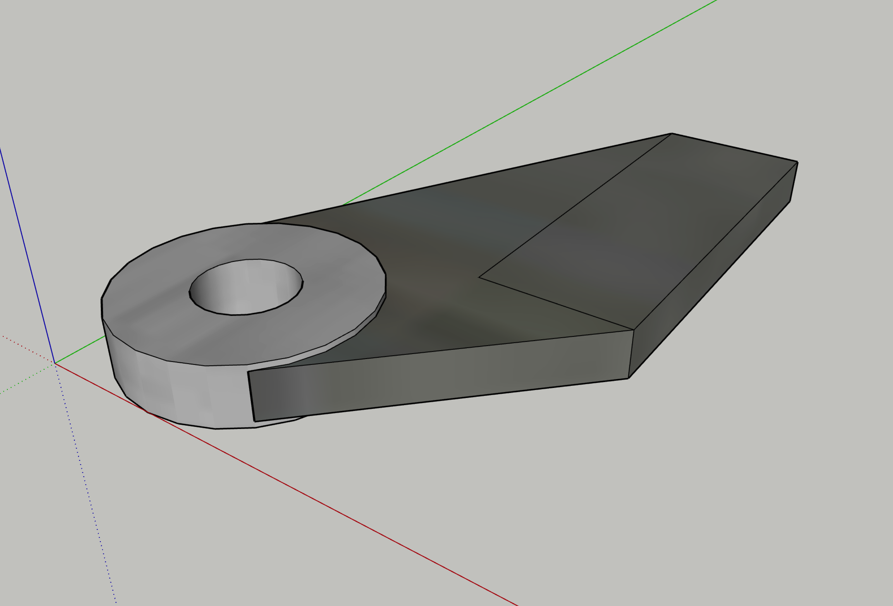
docs/Undercarriage/09-Pivot-Bottom.png
