p2made/P2-Camp-Kitchen/docs/Undercarriage/10-Pivot-Spacer.png

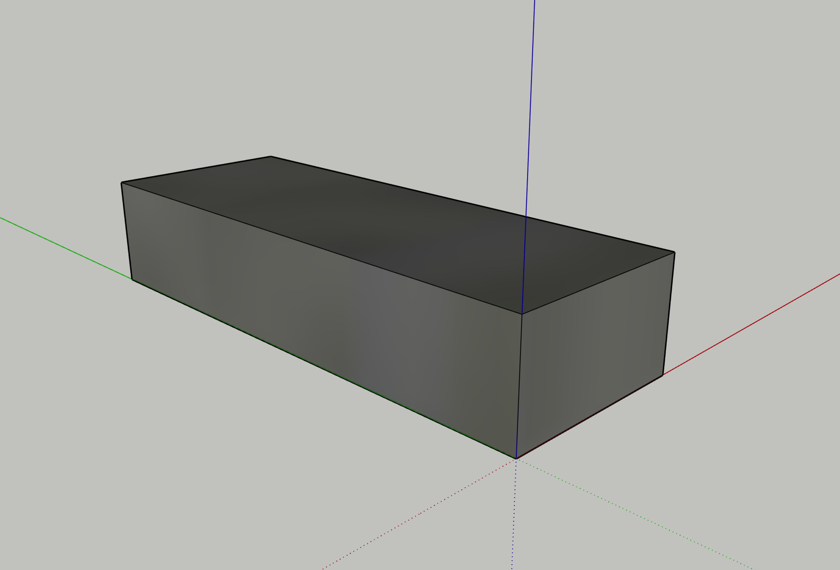
docs/Undercarriage/10-Pivot-Spacer.png
