p2made/P2-Camp-Kitchen/Kitchen-on-Challenger-1.png

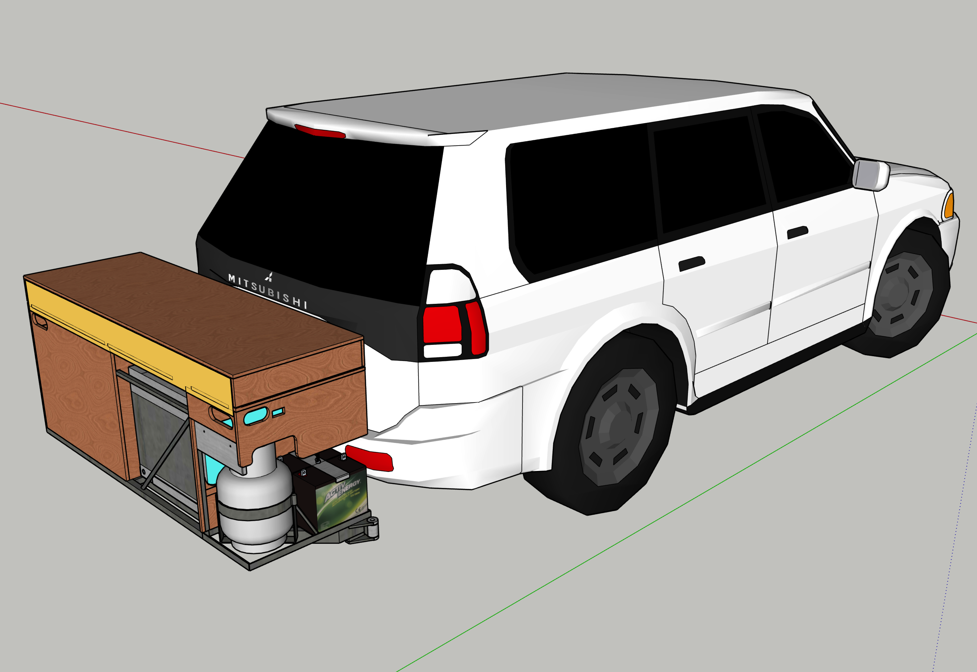
Kitchen-on-Challenger-1.png
