p2made/P2-Camp-Kitchen/Kitchen-on-Challenger-2.png

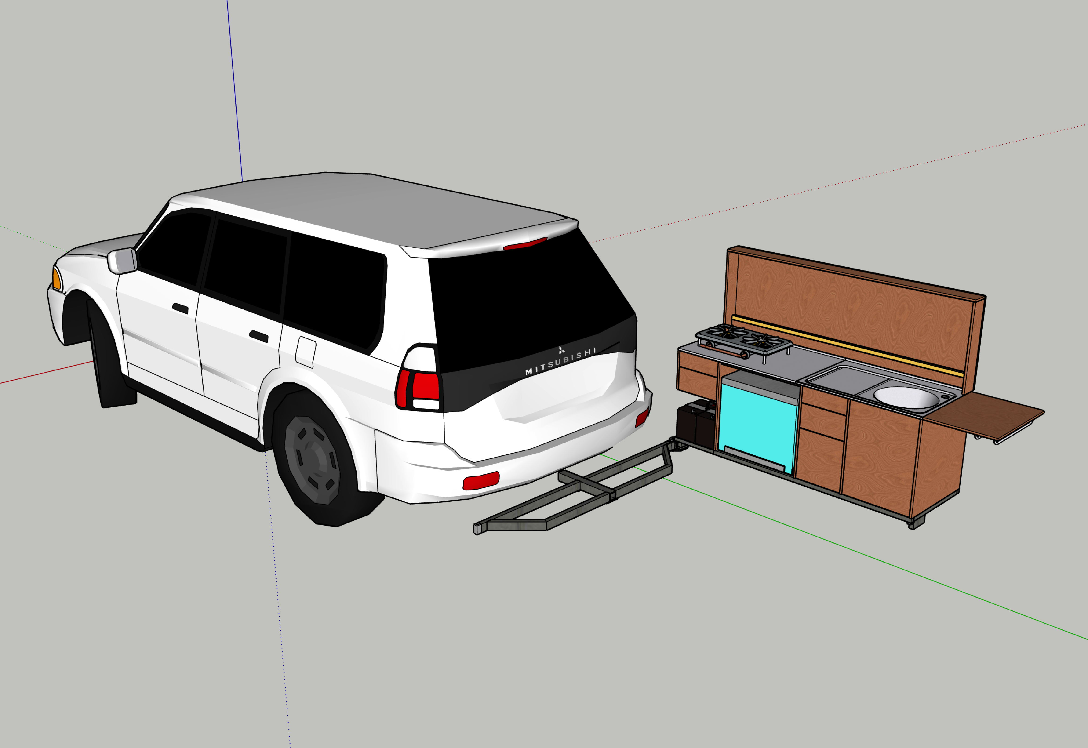
Kitchen-on-Challenger-2.png
